braille-systems/braille-trainer/doc/fab_school_intro/pictures/braille.jpg

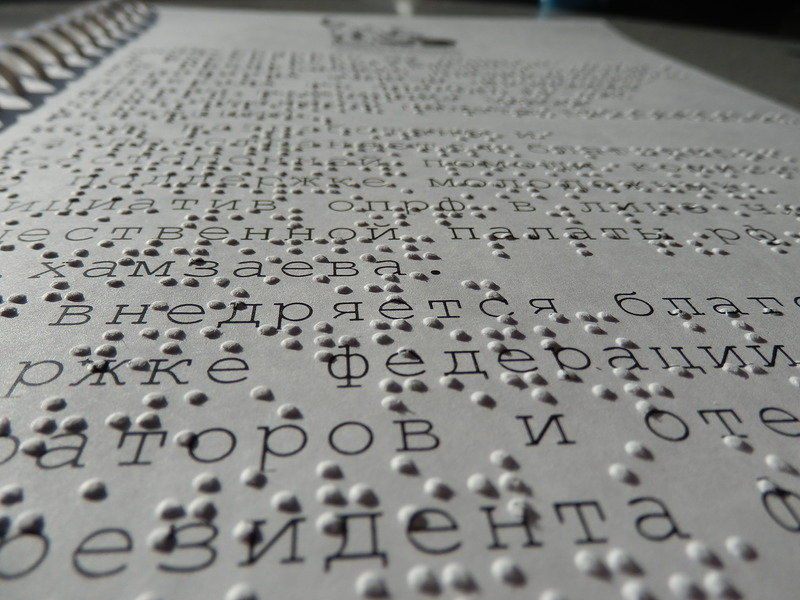
doc/fab_school_intro/pictures/braille.jpg
