braille-systems/braille-trainer/doc/fab_school_intro/pictures/contact.jpg

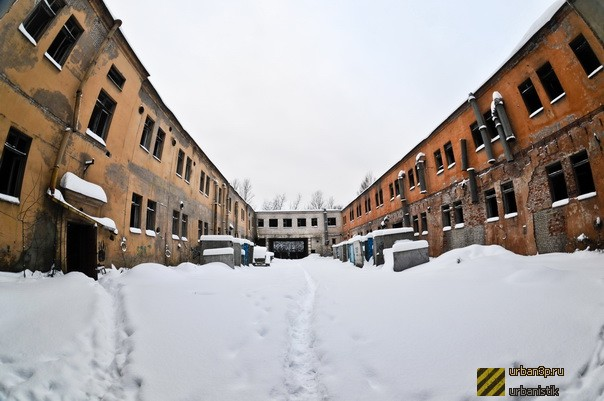
doc/fab_school_intro/pictures/contact.jpg
