braille-systems/braille-trainer/doc/prev_studies/IMG_0652.jpg

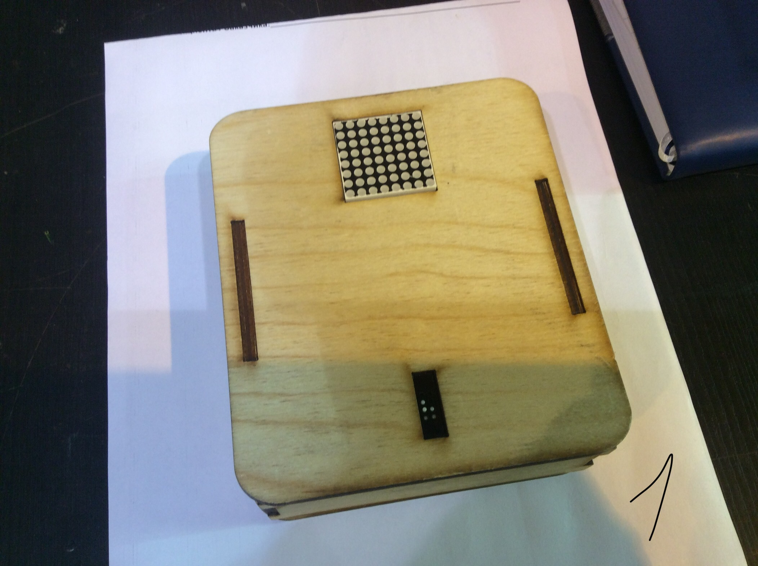
doc/prev_studies/IMG_0652.jpg
