braille-systems/braille-trainer/doc/prev_studies/IMG_0653.jpg

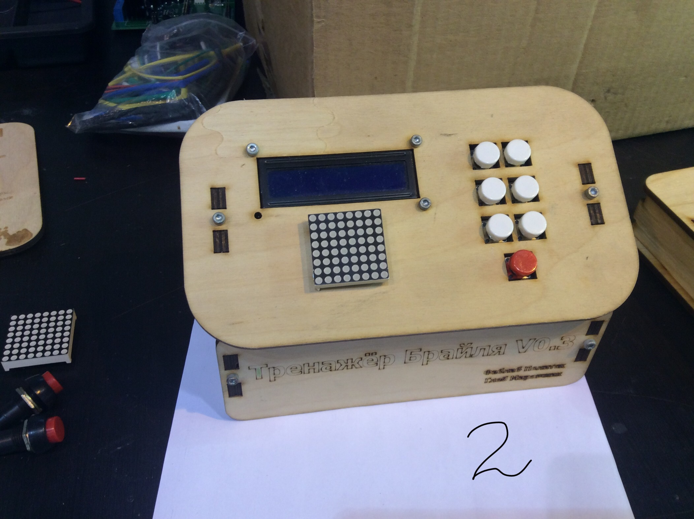
doc/prev_studies/IMG_0653.jpg
