braille-systems/braille-trainer/doc/prev_studies/IMG_0654.jpg

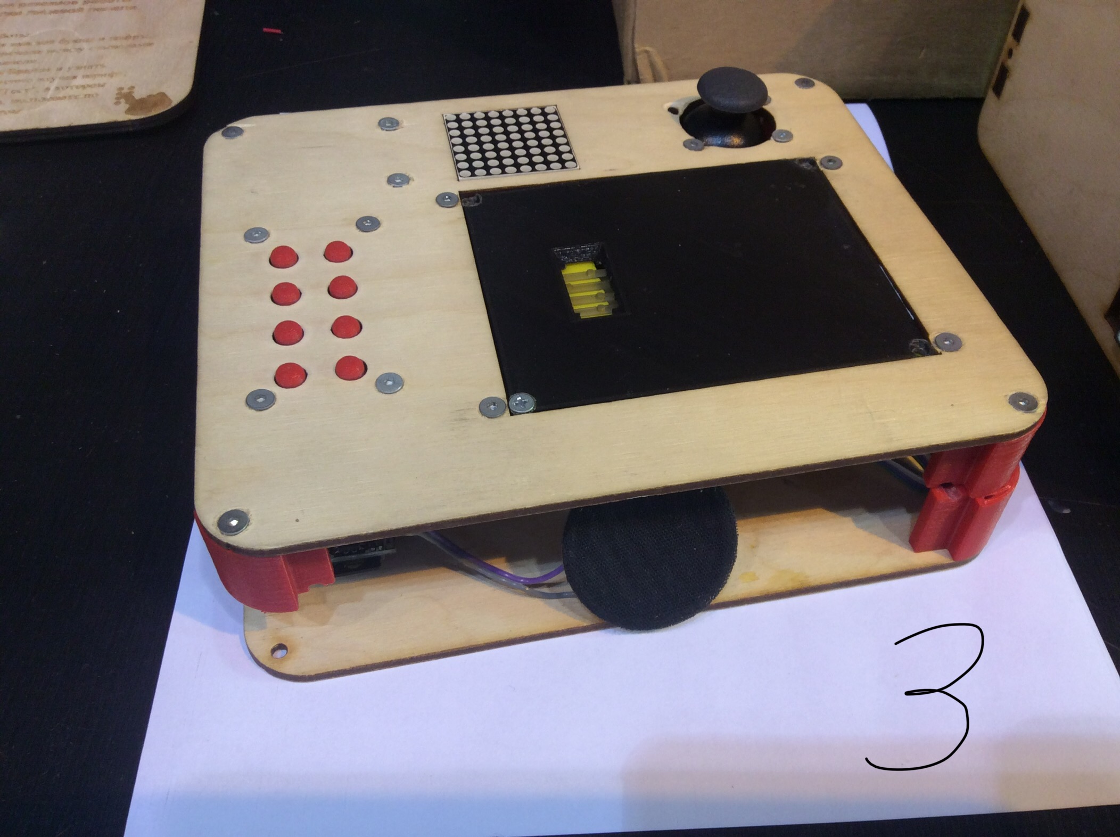
doc/prev_studies/IMG_0654.jpg
