braille-systems/braille-trainer/doc/prev_studies/IMG_0655.jpg

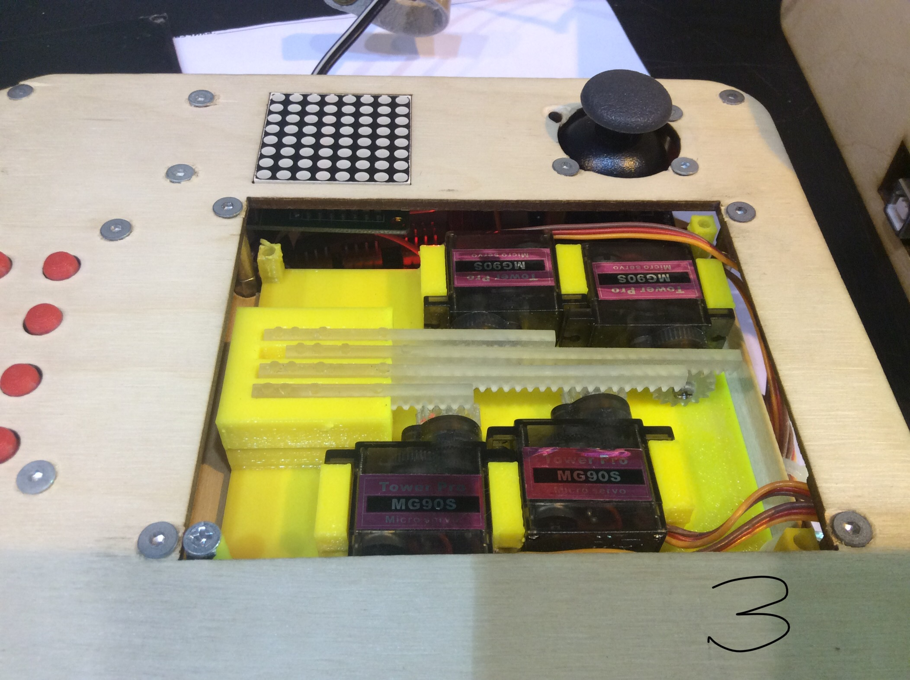
doc/prev_studies/IMG_0655.jpg
