braille-systems/braille-trainer/doc/prev_studies/IMG_0656.jpg

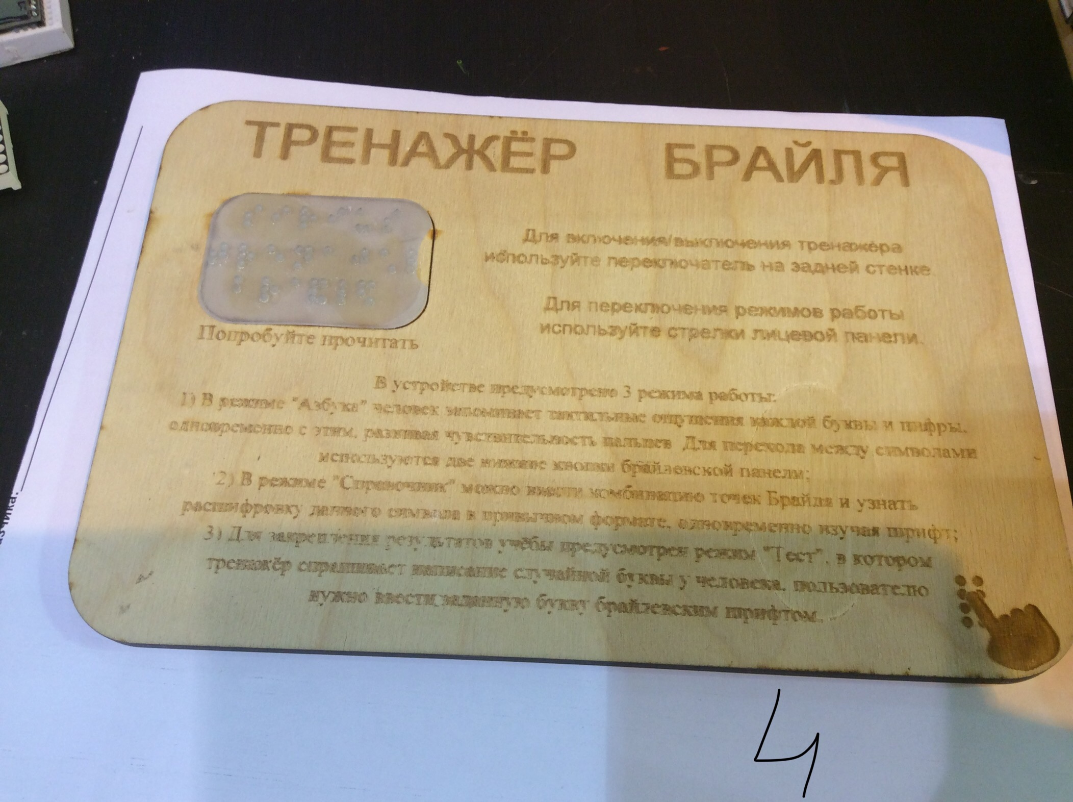
doc/prev_studies/IMG_0656.jpg
