braille-systems/braille-trainer/doc/prev_studies/IMG_0657.jpg

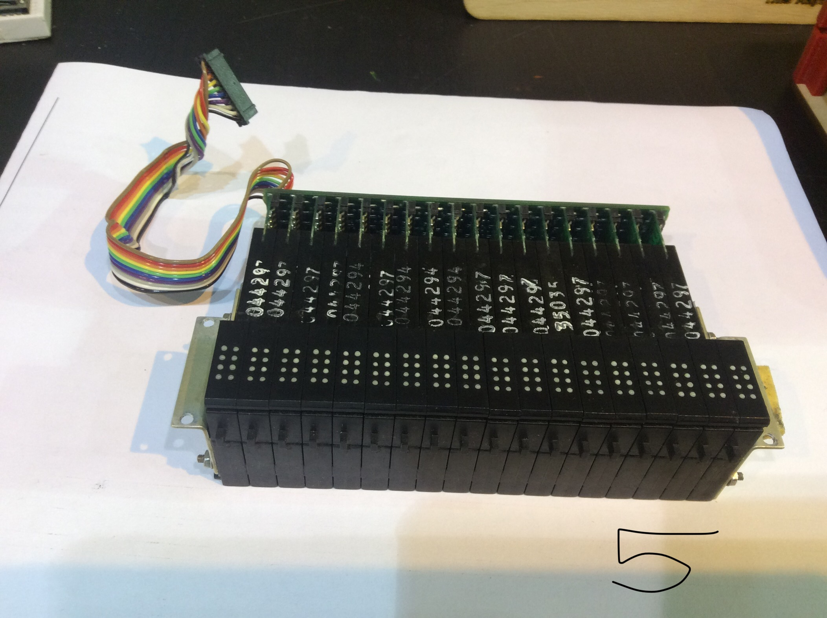
doc/prev_studies/IMG_0657.jpg
