braille-systems/braille-trainer/doc/prev_studies/IMG_0658.jpg

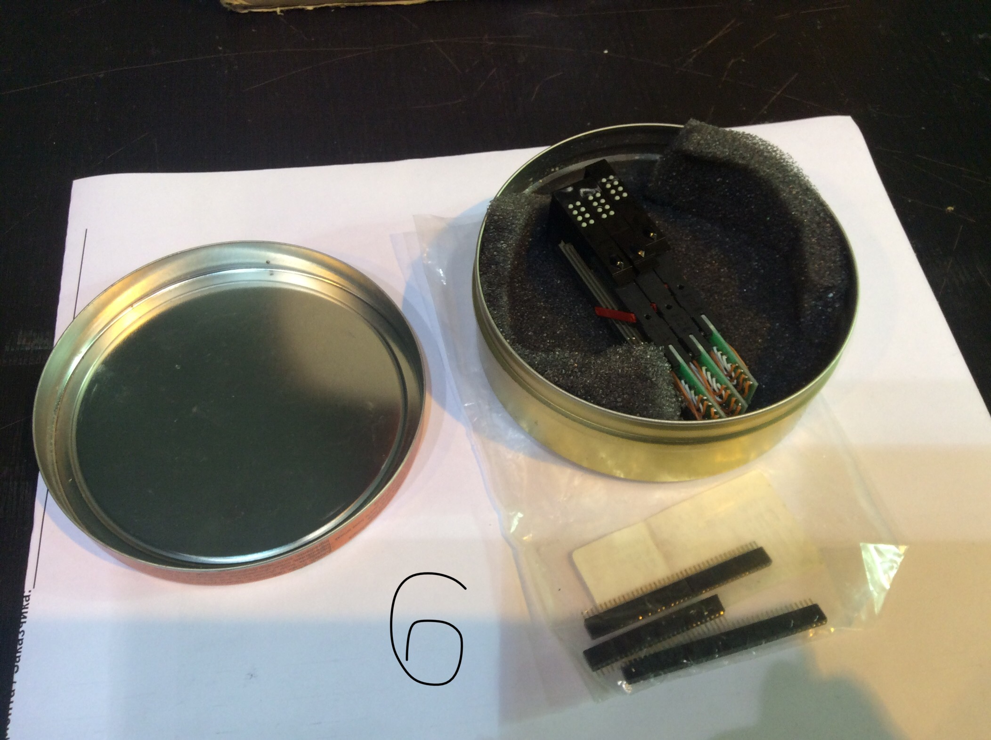
doc/prev_studies/IMG_0658.jpg
