braille-systems/braille-trainer/parts/stl2/drumstick.STL

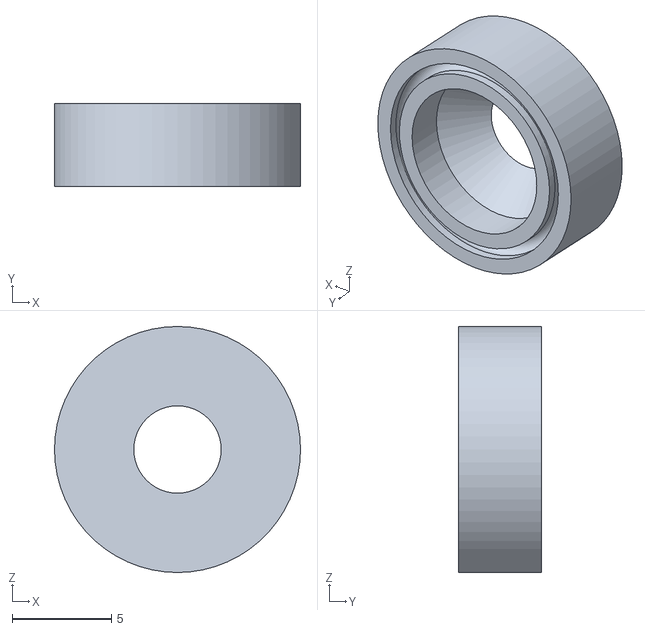
[picture p27: CAD file, 2019-05-09]
parts/stl2/drumstick.STL
12.4 x 4.20 x 12.4
