braille-systems/braille-trainer/parts/dxf2/side-long-back.DXF

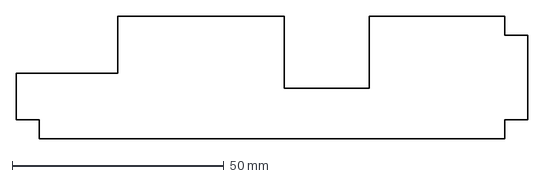
[picture p28: CAD file, 2019-03-31]
parts/dxf2/side-long-back.DXF
121.0 x 29.0 mm
