braille-systems/braille-trainer/parts/stl2/usbNest.STL

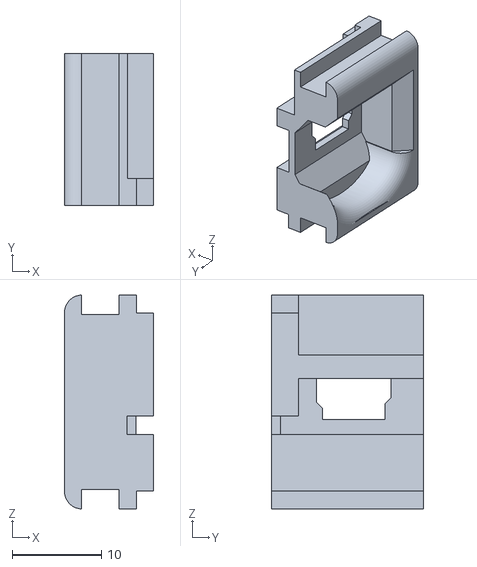
[picture p29: CAD file, 2019-05-09]
parts/stl2/usbNest.STL
10.00 x 17.0 x 24.0
