braille-systems/braille-trainer/parts/dxf2/side-2-button.DXF

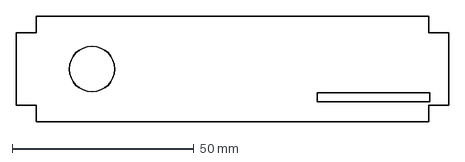
[picture p30: CAD file, 2019-03-31]
parts/dxf2/side-2-button.DXF
119.0 x 29.0 mm
