braille-systems/braille-trainer/parts/stl2/space_housing.STL

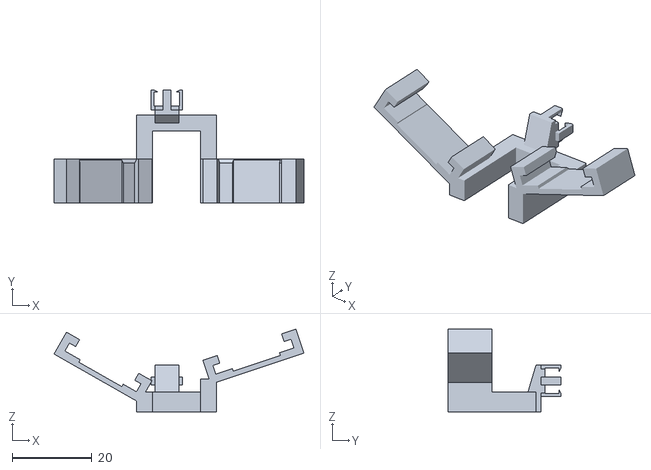
[picture p31: CAD file, 2019-05-09]
parts/stl2/space_housing.STL
62.6 x 28.2 x 20.7
