braille-systems/braille-trainer/parts/dxf2/side-1.DXF

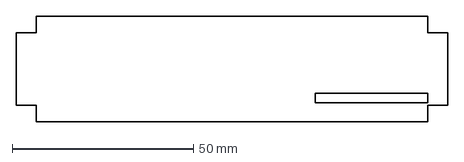
[picture p32: CAD file, 2019-03-31]
parts/dxf2/side-1.DXF
119.0 x 29.0 mm
