braille-systems/braille-trainer/parts/stl2/space.STL

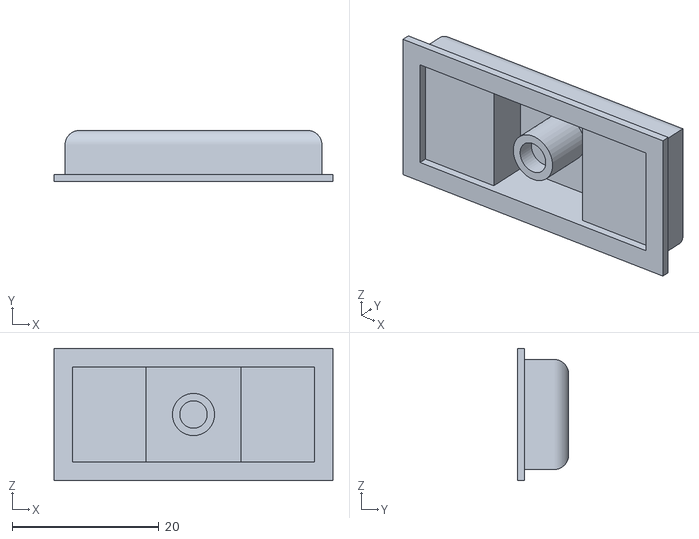
[picture p33: CAD file, 2019-05-09]
parts/stl2/space.STL
38.0 x 7.00 x 18.0
