braille-systems/braille-trainer/parts/stl2/corner_joystick.STL

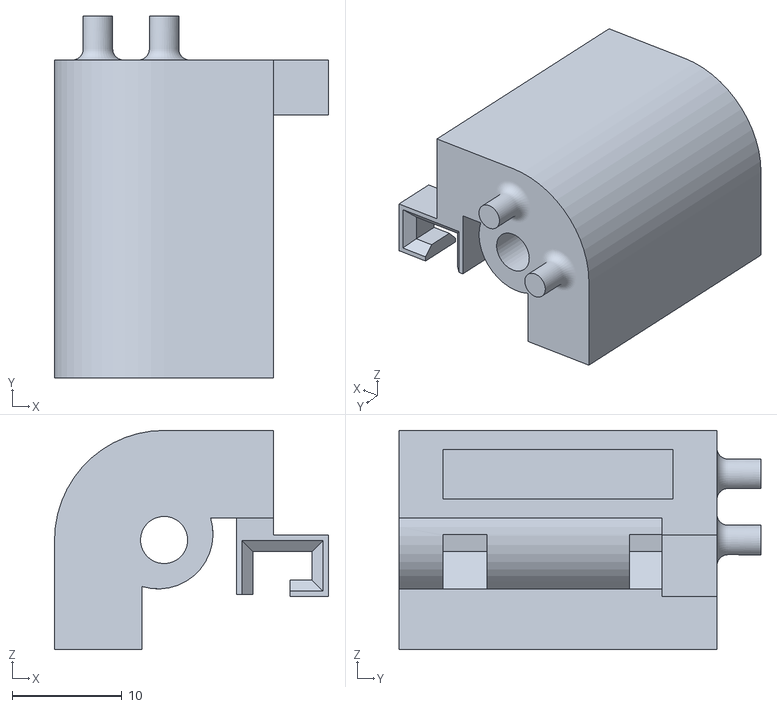
[picture p34: CAD file, 2019-04-06]
parts/stl2/corner_joystick.STL
25.0 x 33.0 x 20.0
