braille-systems/braille-trainer/parts/stl2/corner_pwm.STL

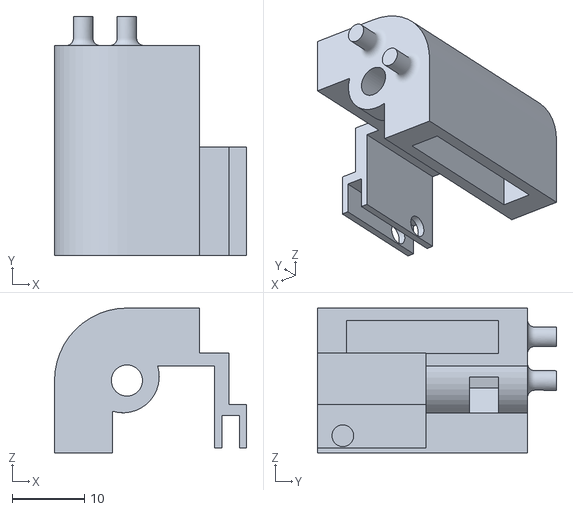
[picture p35: CAD file, 2019-04-06]
parts/stl2/corner_pwm.STL
26.5 x 33.0 x 20.0
