braille-systems/braille-trainer/parts/stl2/support.STL

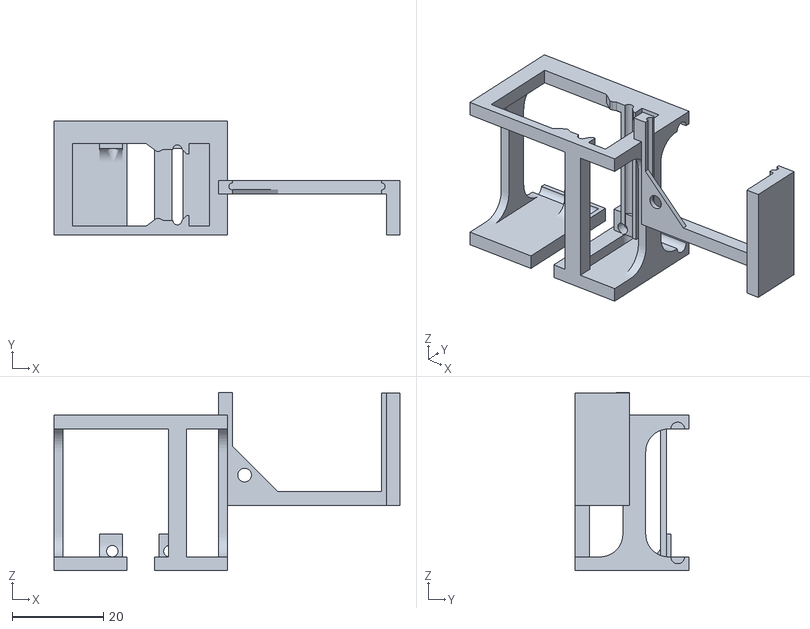
[picture p36: CAD file, 2019-03-31]
parts/stl2/support.STL
75.7 x 25.0 x 39.0
