braille-systems/braille-trainer/parts/stl2/corner.STL

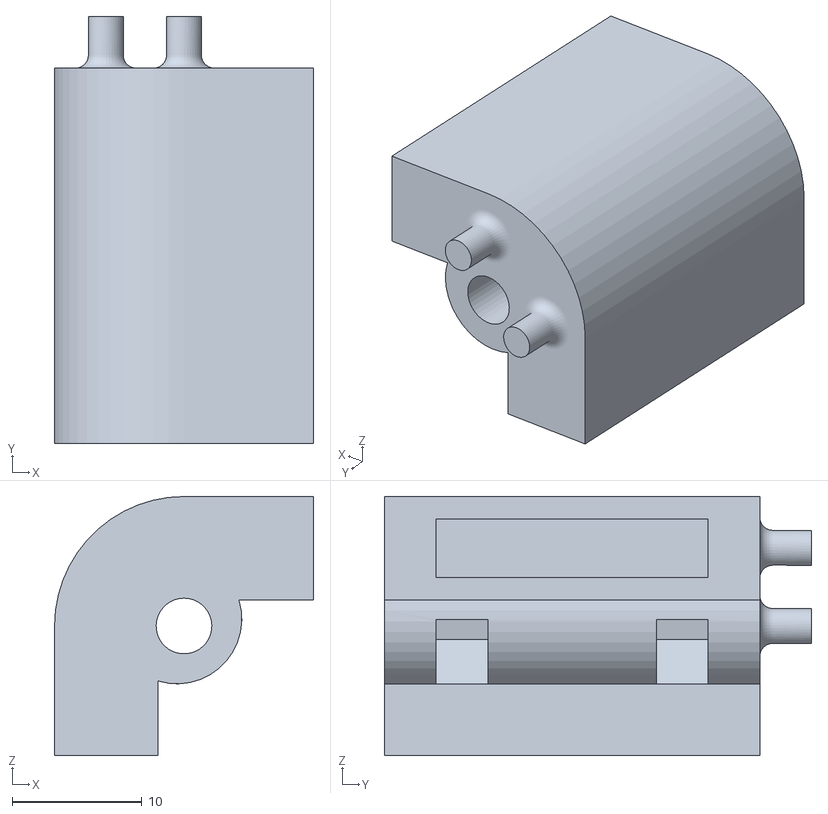
[picture p37: CAD file, 2019-03-31]
parts/stl2/corner.STL
20.0 x 33.0 x 20.0
