braille-systems/braille-trainer/parts/stl2/corner_speaker.STL

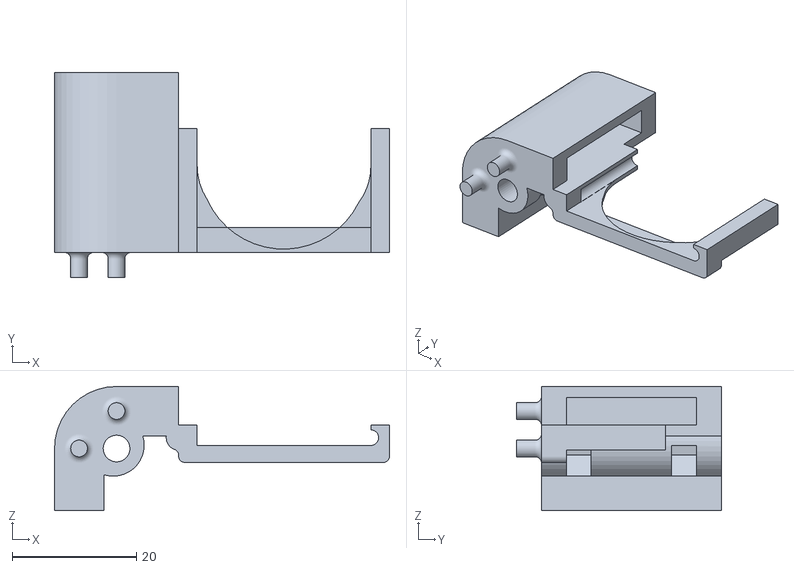
[picture p38: CAD file, 2019-03-31]
parts/stl2/corner_speaker.STL
54.0 x 33.0 x 20.0
