braille-systems/braille-trainer/parts/stl2/chocolate_hotfix.STL

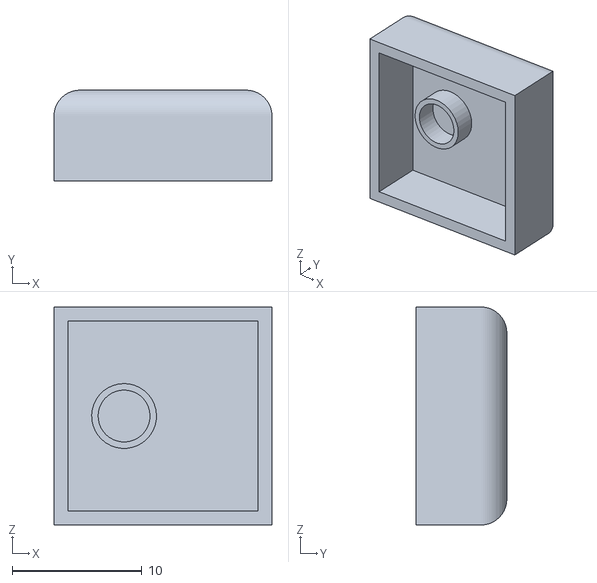
[picture p39: CAD file, 2019-02-16]
parts/stl2/chocolate_hotfix.STL
16.8 x 7.00 x 16.8
