braille-systems/braille-trainer/parts/solidworks/bearing_shaft.sldprt

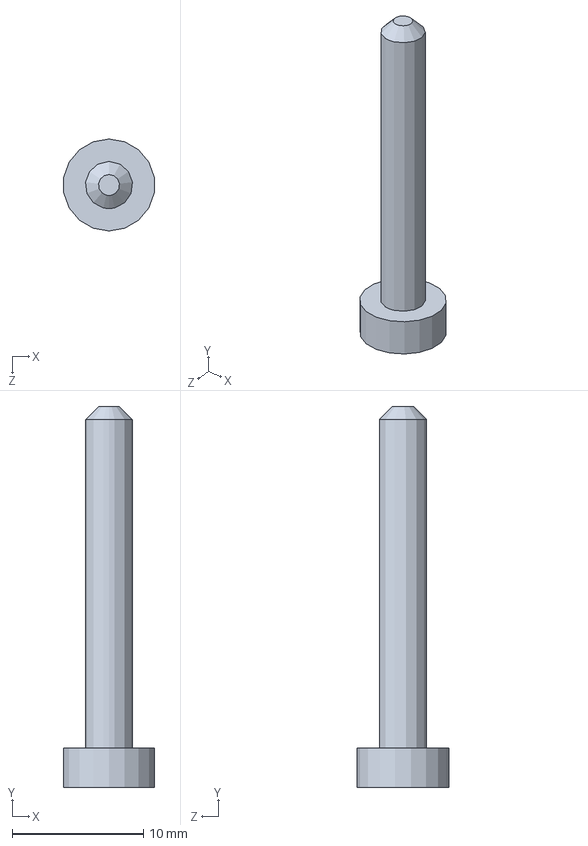
[picture p40: CAD file, 2019-02-04]
parts/solidworks/bearing_shaft.sldprt
6.89 x 29.0 x 7.00 mm
