braille-systems/braille-trainer/parts/solidworks/bearing.sldprt

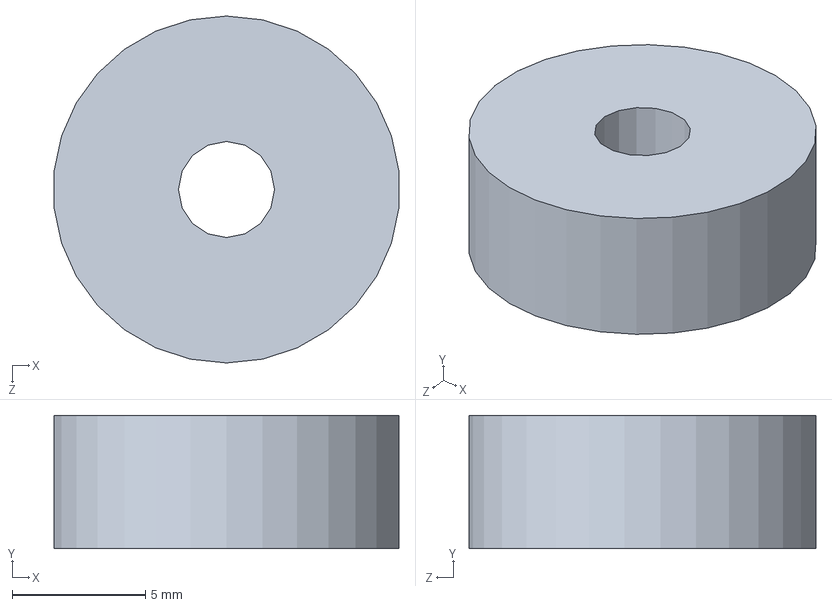
[picture p41: CAD file, 2019-02-04]
parts/solidworks/bearing.sldprt
12.9 x 5.00 x 13.0 mm
