braille-systems/braille-trainer/arduino/printTextPWM/audio_functions.h

#ifndef H_AUDIO_FUNCS
#define H_AUDIO_FUNCS

#include"common_declarations.h"

//джойстик
#define NOTE_B4  494
#define NOTE_C4  262
#define NOTE_A4  440
#define NOTE_E4  330

//кнопка джойстика
#define NOTE_D4  293

//клавиатура
#define NOTE_C3  131
#define NOTE_D3  148
#define NOTE_E3  165
#define NOTE_F3  175
#define NOTE_G3  196
#define NOTE_A3  207

/*
#define NOTE_C3_1  231
#define NOTE_D3_1  248
#define NOTE_E3_1  265
#define NOTE_F3_1  275
#define NOTE_G3_1  296
#define NOTE_A3_1  307
 */
 
int muteButtonState;
unsigned long timingSpeak; //тайминг динамика

void alert(int type) {      //сигнал
  int note = 0;
  switch(type) {
    case 'l':
      note = NOTE_C4;
      break;
    case 'r':
      note = NOTE_A4;
      break;
    case 'd':
      note = NOTE_E4;
      break;
    case 'u':
      note = NOTE_B4;
      break;
      
    case 'c':
      note = NOTE_B4;
      break;
      
    case 'a':
      note = NOTE_C3;
      break;
    case 'b':
      note = NOTE_D3;
      break;
    case 'e':
      note = NOTE_E3;
      break;
    case 'f':
      note = NOTE_F3;
      break;
    case 'g':
      note = NOTE_G3;
      break;
    case 'h':
      note = NOTE_A3;
      break;
//    case 'i':
//      note = ...;
//      break;
  }
  tone(speaker, note, 100);
  timingSpeak = millis();
  while(millis() - timingSpeak < 100);
  noTone(speaker);
}

#endif
